MOSH-Insa-Toulouse/2023-2024-4GP-LE-BLANC--PERALES-RIOS/Android_app/Android_app_logic_chart.png

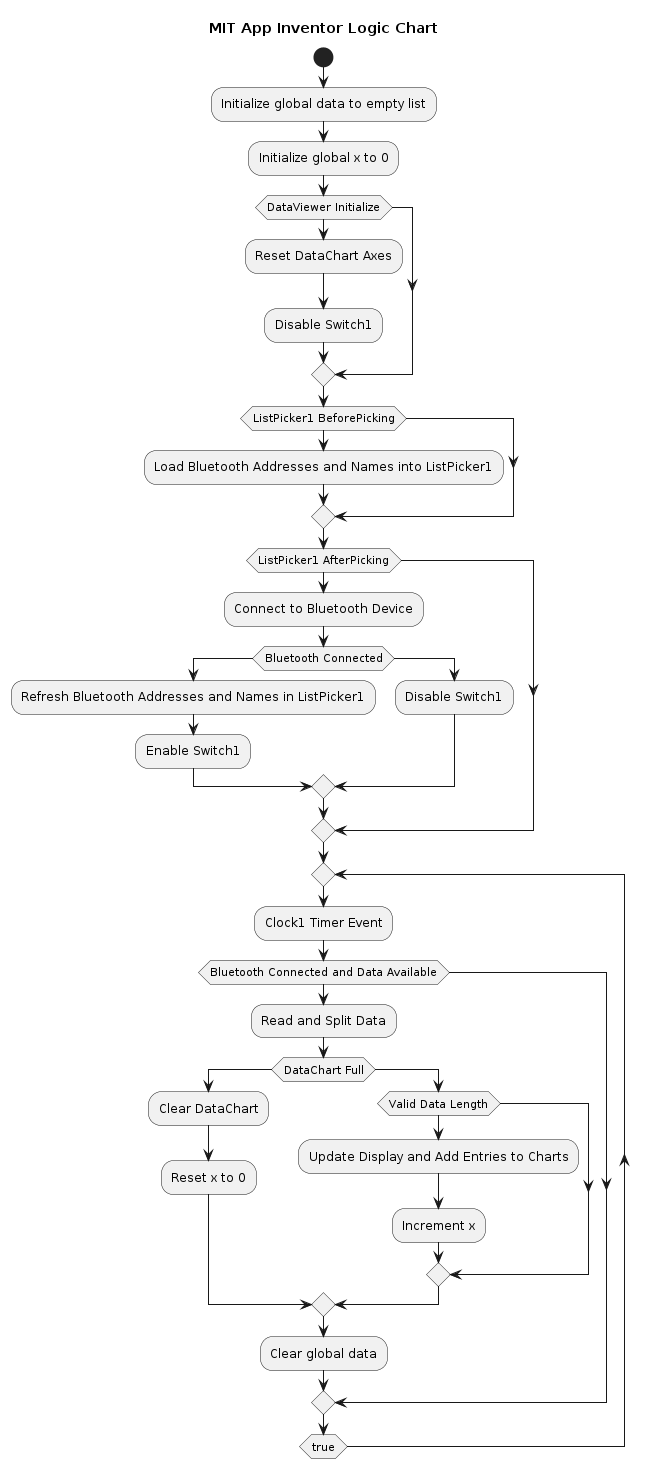
Android_app/Android_app_logic_chart.png
