MOSH-Insa-Toulouse/2023-2024-4GP-LE-BLANC--PERALES-RIOS/Android_app/App_screen.png

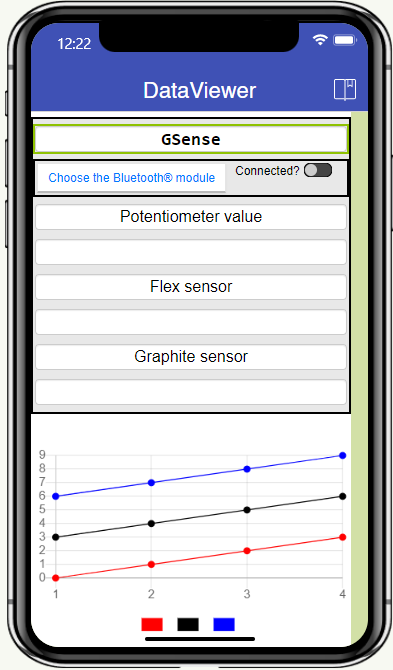
Android_app/App_screen.png
