MOSH-Insa-Toulouse/2023-2024-4GP-LE-BLANC--PERALES-RIOS/Android_app/Code_blocks_app (2).png

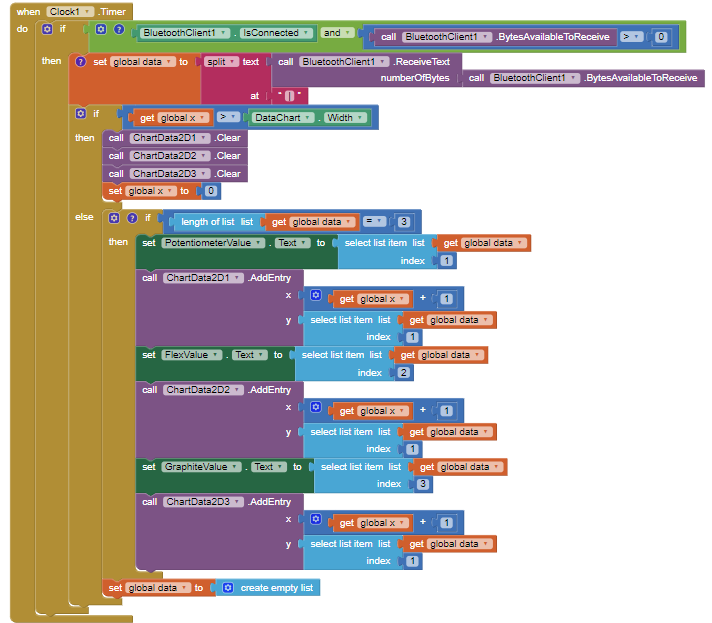
Android_app/Code_blocks_app (2).png
