MOSH-Insa-Toulouse/2023-2024-4GP-LE-BLANC--PERALES-RIOS/Arduino code/Arduino_code_logic_chart.png

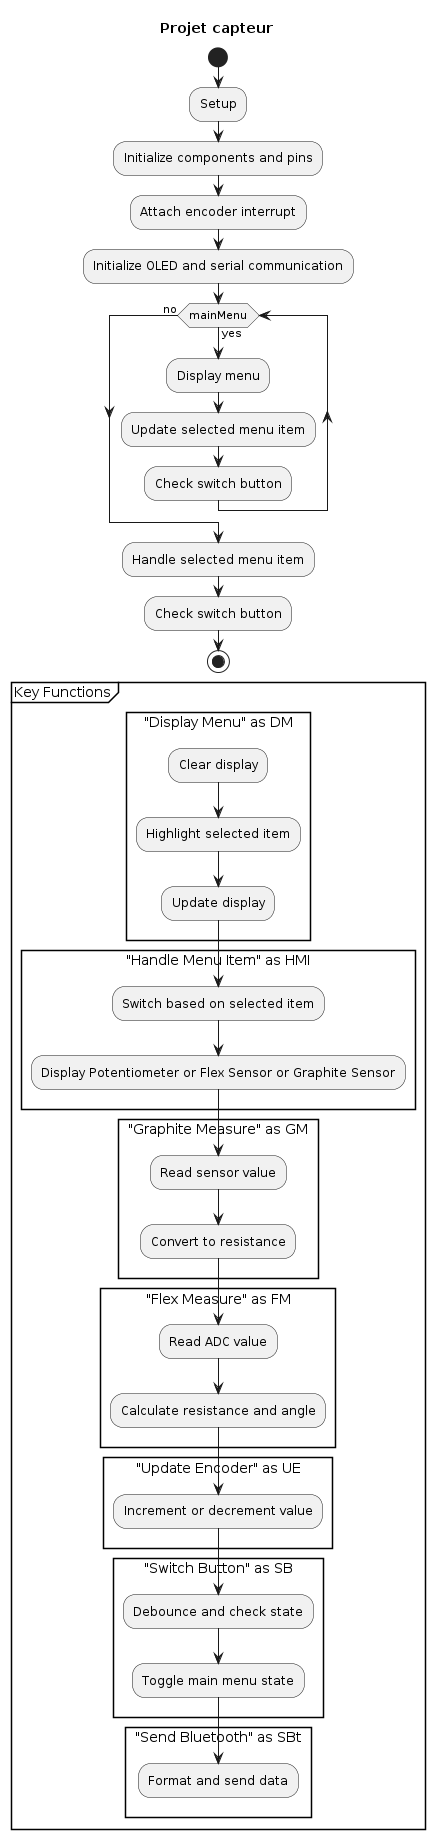
Arduino code/Arduino_code_logic_chart.png
