MOSH-Insa-Toulouse/2023-2024-4GP-LE-BLANC--PERALES-RIOS/Arduino code/Menu_graphite_sensor.jpg

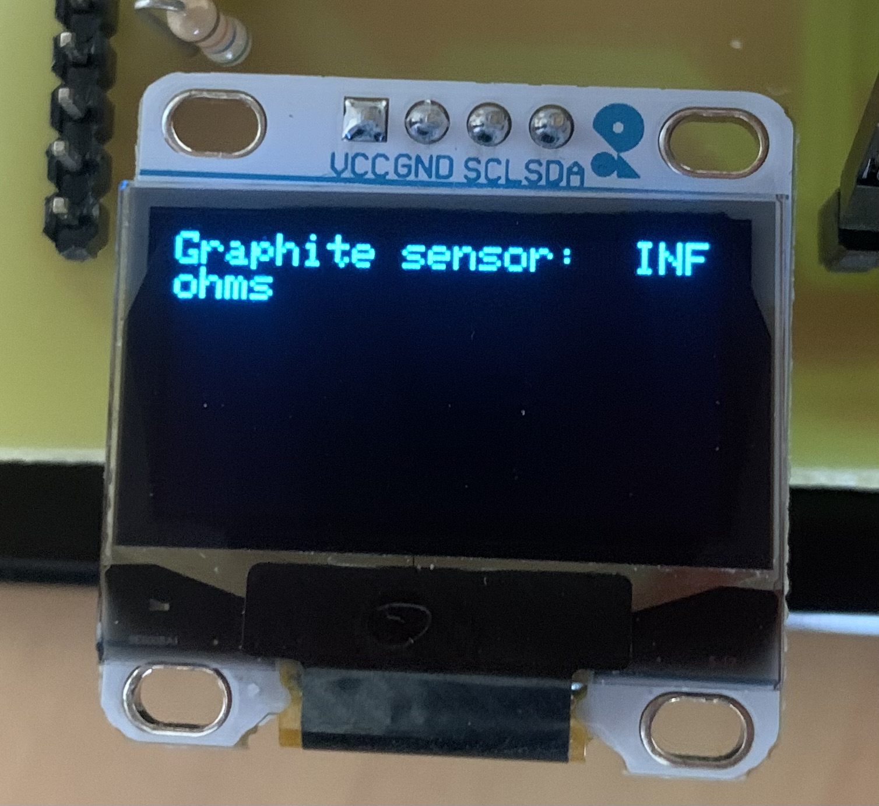
Arduino code/Menu_graphite_sensor.jpg
