MOSH-Insa-Toulouse/2023-2024-4GP-LE-BLANC--PERALES-RIOS/Arduino code/Menu_potentiometer.jpg

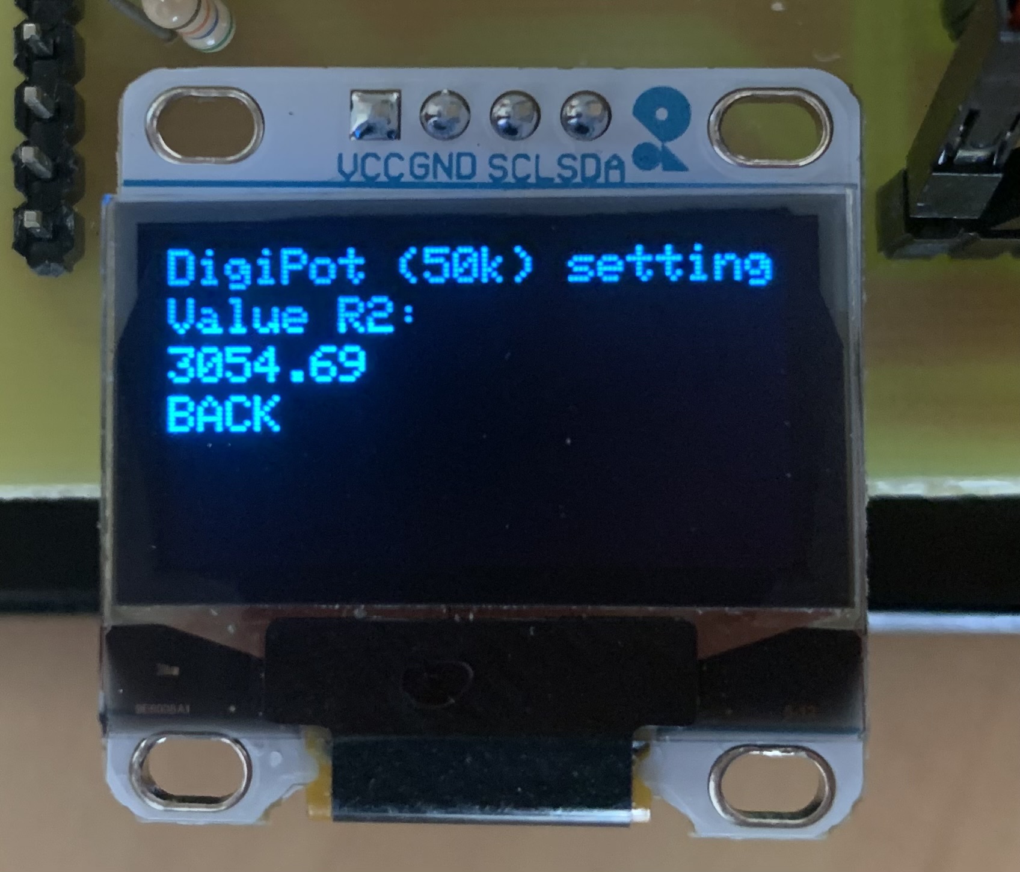
Arduino code/Menu_potentiometer.jpg
