MOSH-Insa-Toulouse/2023-2024-4GP-LE-BLANC--PERALES-RIOS/Images/Code_blocks_app_with_login (2).png

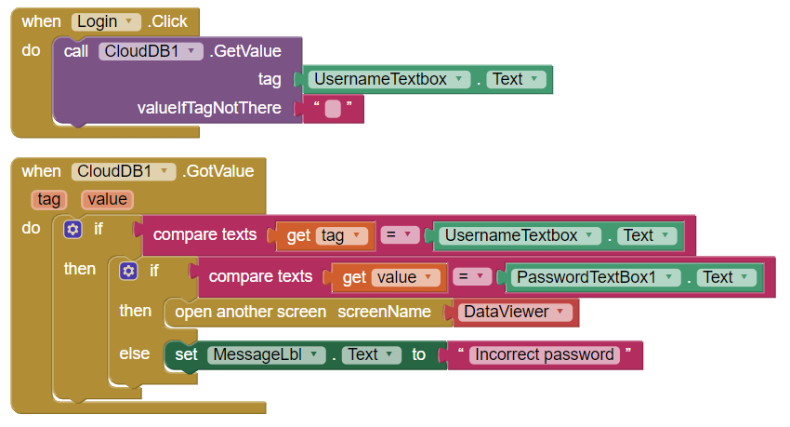
Images/Code_blocks_app_with_login (2).png
