MOSH-Insa-Toulouse/2023-2024-4GP-LE-BLANC--PERALES-RIOS/Images/Flex_sensor.jpg

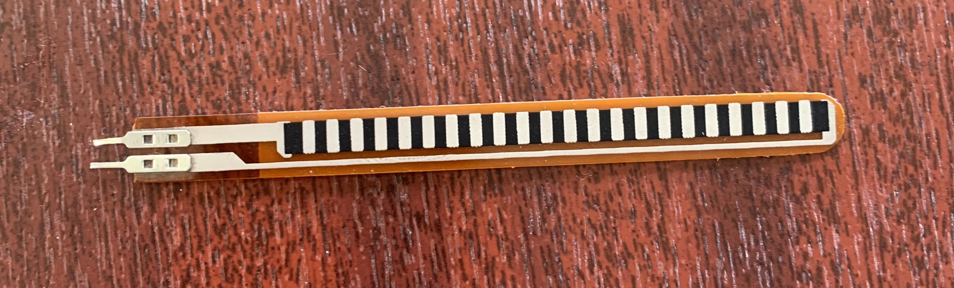
Images/Flex_sensor.jpg
