MOSH-Insa-Toulouse/2023-2024-4GP-LE-BLANC--PERALES-RIOS/Images/MCP4150_3D_view.png

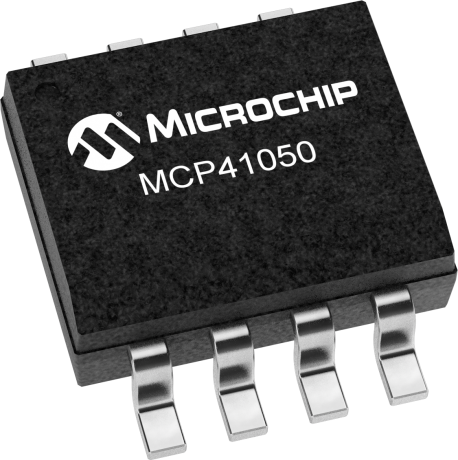
Images/MCP4150_3D_view.png
