MOSH-Insa-Toulouse/2023-2024-4GP-LE-BLANC--PERALES-RIOS/Images/Physical_explanation_resistance.png

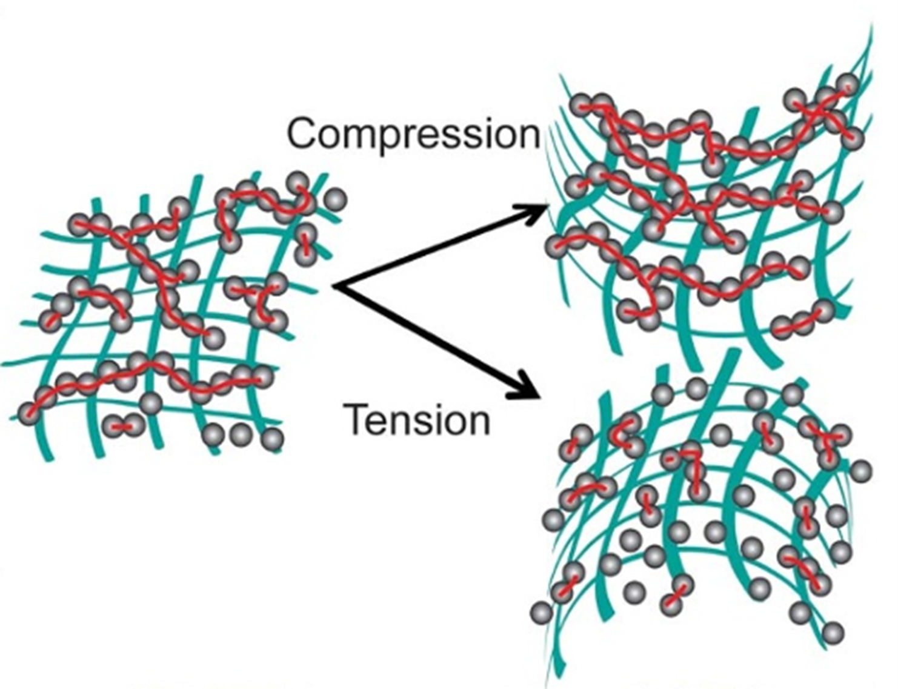
Images/Physical_explanation_resistance.png
