MOSH-Insa-Toulouse/2023-2024-4GP-LE-BLANC--PERALES-RIOS/Images/Rotary_encoder_KY041.jpg

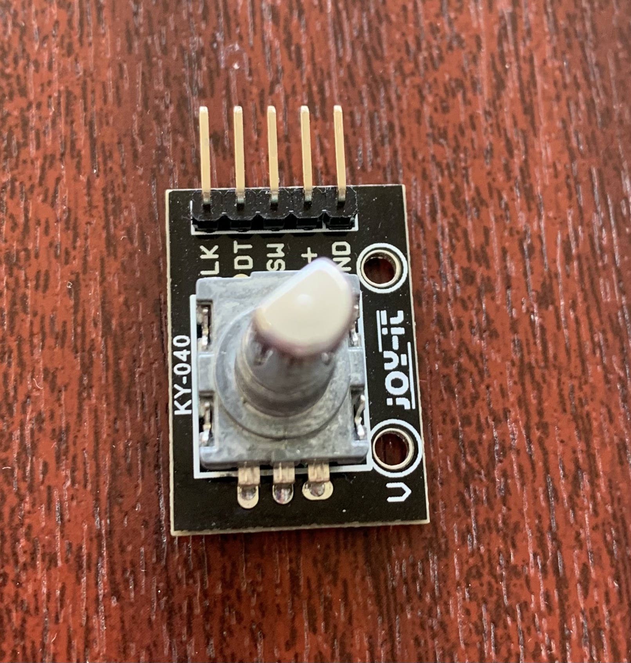
Images/Rotary_encoder_KY041.jpg
