MOSH-Insa-Toulouse/2023-2024-4GP-LE-BLANC--PERALES-RIOS/KiCAD_PCB/3D_models/rotary encoder step files/Step Files/decal_encoder.stp

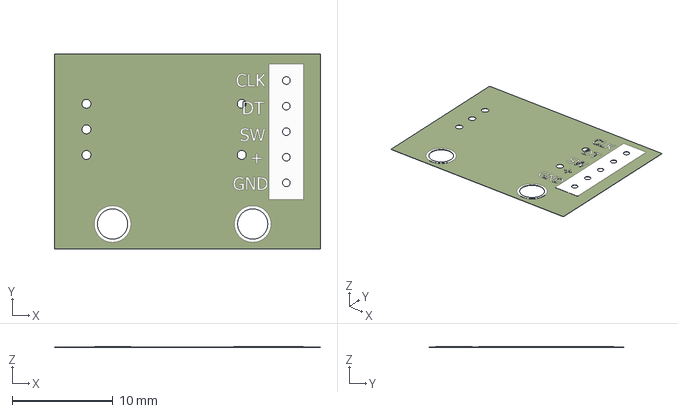
[picture p37: CAD file, 2024-04-05]
KiCAD_PCB/3D_models/rotary encoder step files/Step Files/decal_encoder.stp
26.4 x 19.3 x 0.0508 mm
