MOSH-Insa-Toulouse/2023-2024-4GP-LE-BLANC--PERALES-RIOS/KiCAD_PCB/3D_models/rotary encoder step files/Step Files/mtg flange.stp

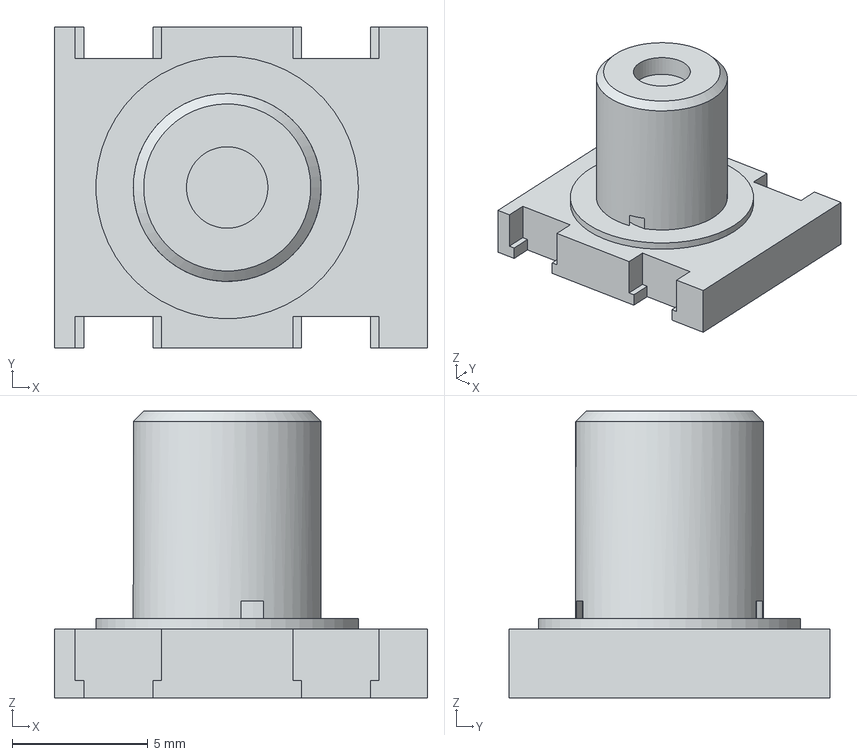
[picture p38: CAD file, 2024-04-05]
KiCAD_PCB/3D_models/rotary encoder step files/Step Files/mtg flange.stp
13.7 x 11.8 x 10.5 mm
