MOSH-Insa-Toulouse/2023-2024-4GP-LE-BLANC--PERALES-RIOS/KiCAD_PCB/3D_models/MCP41050-I_P.STEP

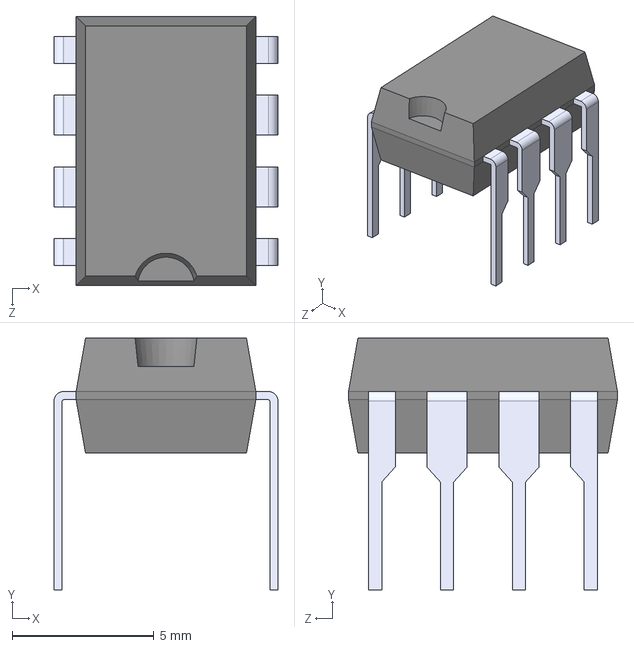
[picture p39: CAD file, 2024-04-05]
KiCAD_PCB/3D_models/MCP41050-I_P.STEP
7.91 x 8.89 x 9.50 mm
