MOSH-Insa-Toulouse/2023-2024-4GP-LE-BLANC--PERALES-RIOS/Bench_test/Deformation_tension.jpg

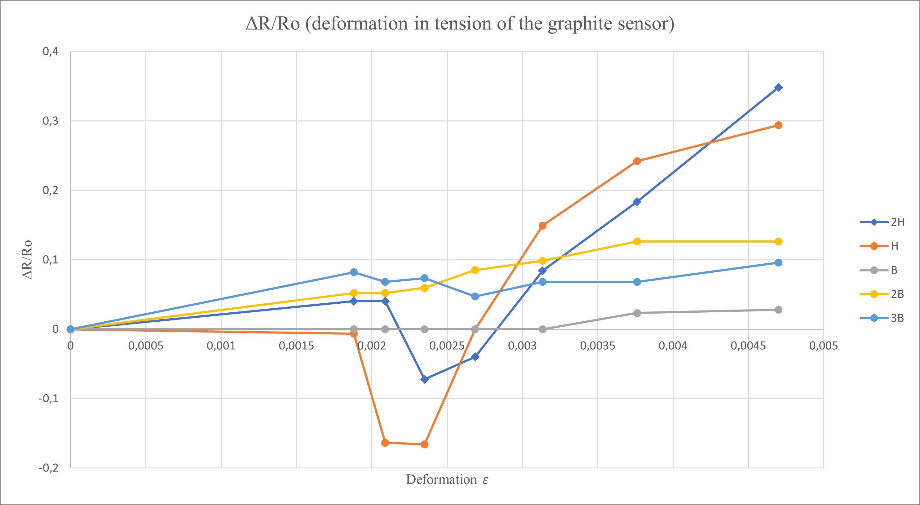
Bench_test/Deformation_tension.jpg
