MOSH-Insa-Toulouse/2023-2024-4GP-LE-BLANC--PERALES-RIOS/Bench_test/Graphite_sensor.png

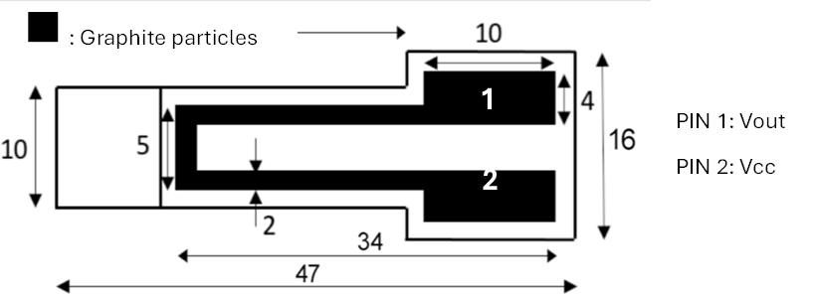
Bench_test/Graphite_sensor.png
