MOSH-Insa-Toulouse/2023-2024-4GP-LE-BLANC--PERALES-RIOS/Bench_test/Sensor_dimensions.png

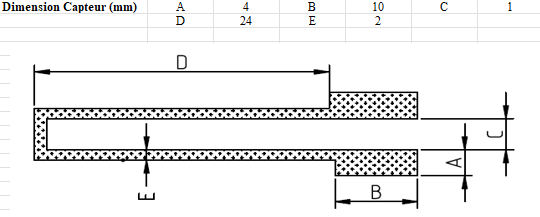
Bench_test/Sensor_dimensions.png
